sunildahiya/atc/Solidworks_Design/cylindrcal shell.SLDPRT

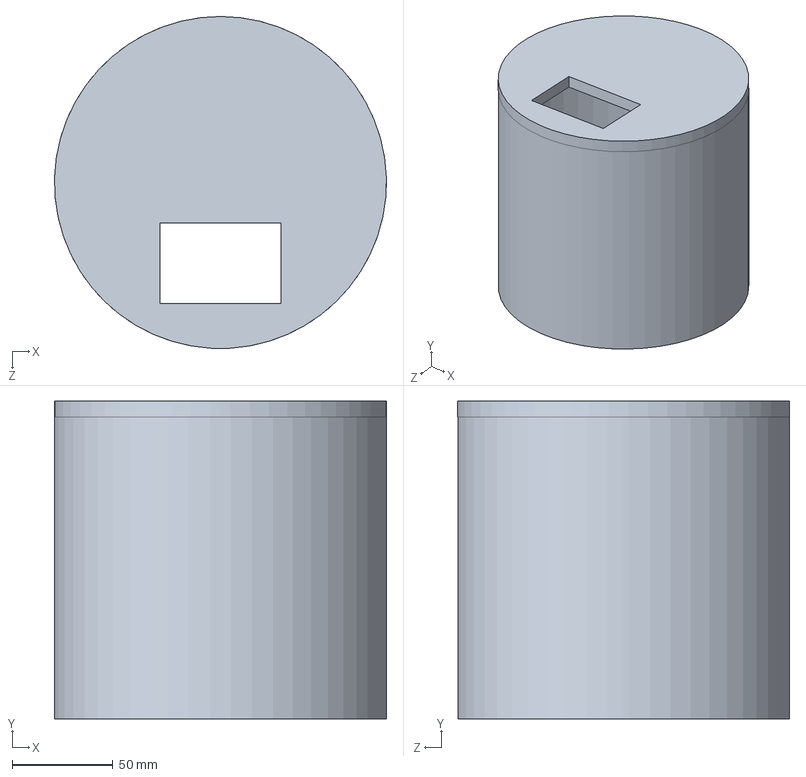
[picture p16: CAD file, 2018-02-13]
Solidworks_Design/cylindrcal shell.SLDPRT
165.0 x 158.0 x 165.0 mm
