sunildahiya/atc/Solidworks_Design/motor_bowl.SLDPRT

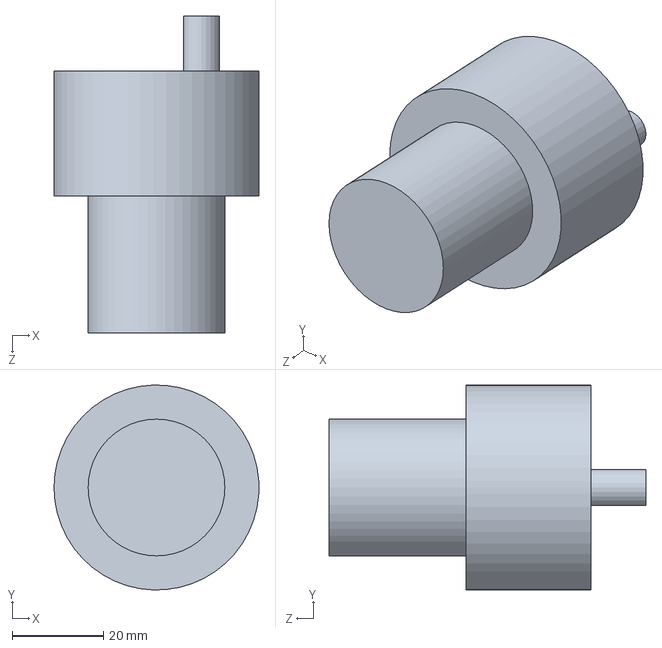
[picture p17: CAD file, 2018-02-13]
Solidworks_Design/motor_bowl.SLDPRT
45.0 x 45.0 x 69.5 mm
