sunildahiya/atc/Solidworks_Design/roller motor.SLDPRT

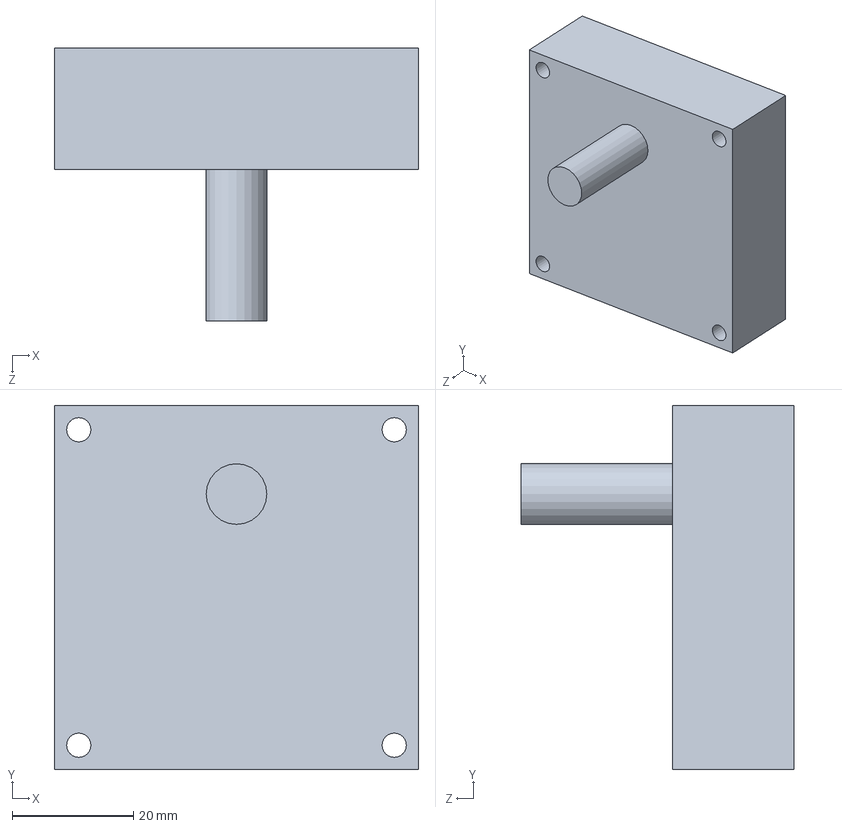
[picture p18: CAD file, 2018-02-13]
Solidworks_Design/roller motor.SLDPRT
60.0 x 60.0 x 45.0 mm
