sunildahiya/atc/Solidworks_Design/OMNI.SLDPRT

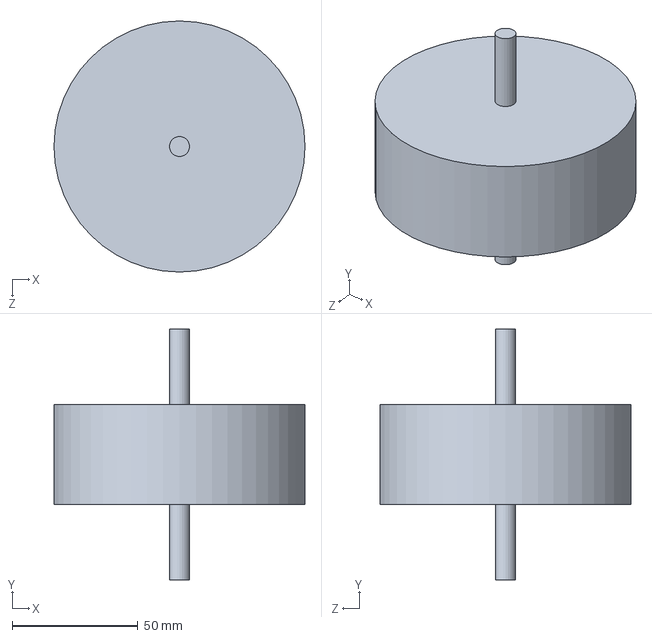
[picture p19: CAD file, 2018-02-13]
Solidworks_Design/OMNI.SLDPRT
100.0 x 100.0 x 100.0 mm
