sunildahiya/atc/Solidworks_Design/wheel.SLDPRT

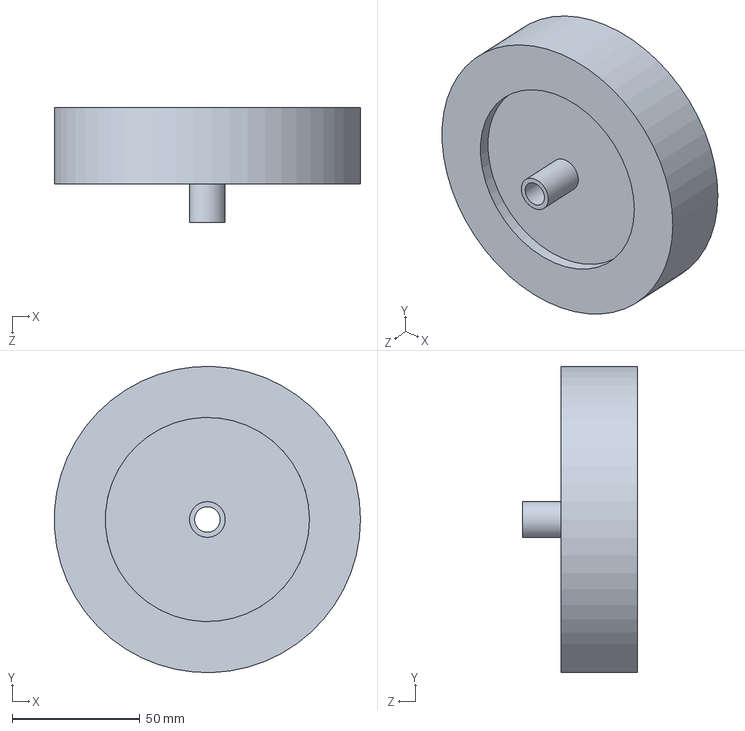
[picture p20: CAD file, 2018-02-13]
Solidworks_Design/wheel.SLDPRT
119.9 x 119.9 x 45.0 mm
