sunildahiya/atc/Solidworks_Design/Chasis.SLDPRT

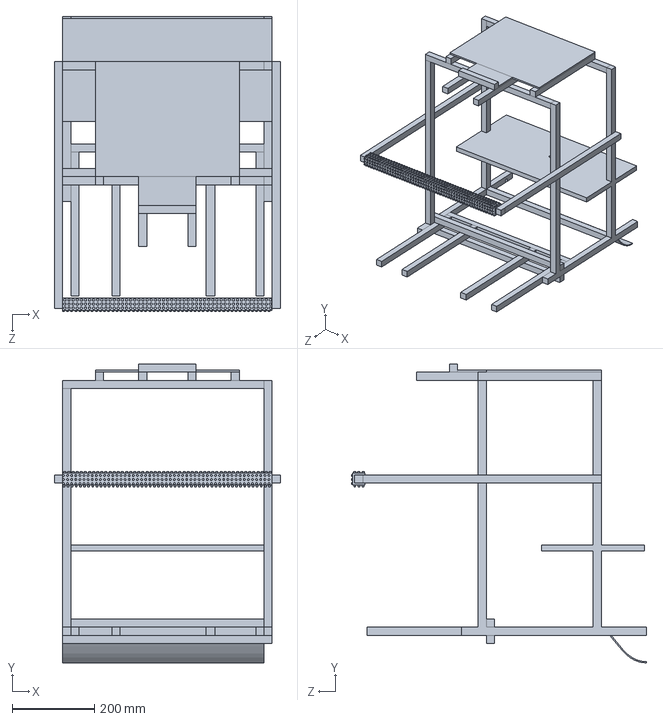
[picture p21: CAD file, 2018-02-13]
Solidworks_Design/Chasis.SLDPRT
550.5 x 727.5 x 718.0 mm
