sunildahiya/atc/Navigation/IMU.ino

void read_imu(){
  jholImu.readGyroData(gyro);
  double dt = micros() - timer;
//  Serial.println(gyro[2]);
//  gyroZangle += dt*(gyro[2]-25050)/131.0/1000000;
  gyroZangle += dt*(gyro[2]-131)/131.0/1000000;
  timer = micros();
  delay(2);
}
